tebl/RetroPanel/gallery/2022-11-07 02.01.57.jpg

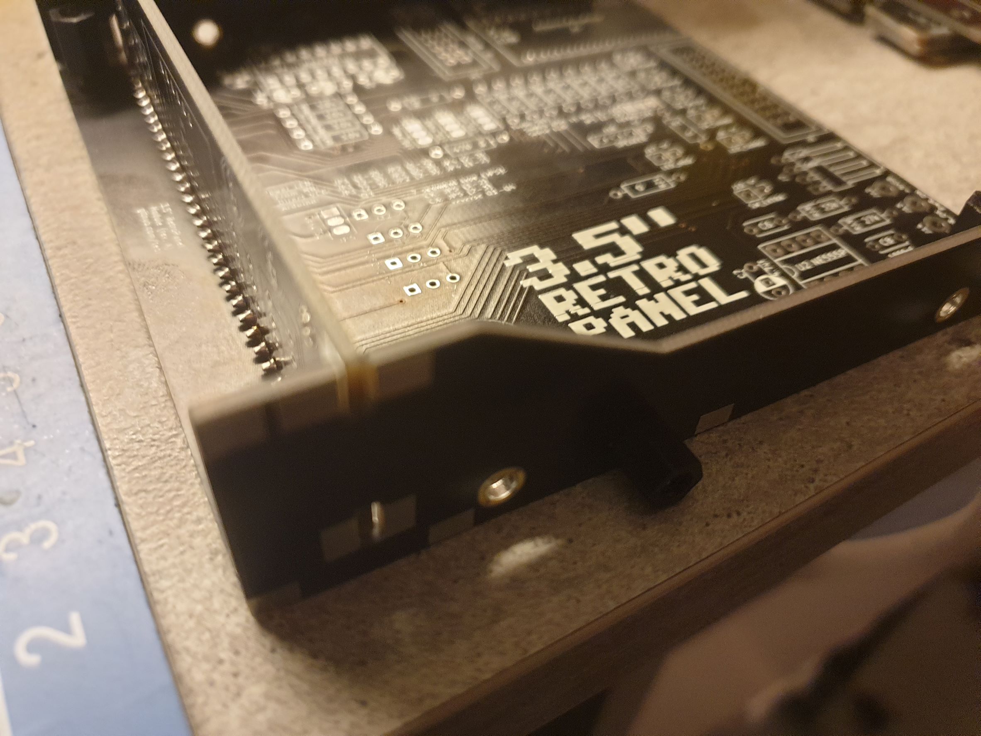
gallery/2022-11-07 02.01.57.jpg
