tebl/RetroPanel/gallery/2022-11-07 02.02.05.jpg

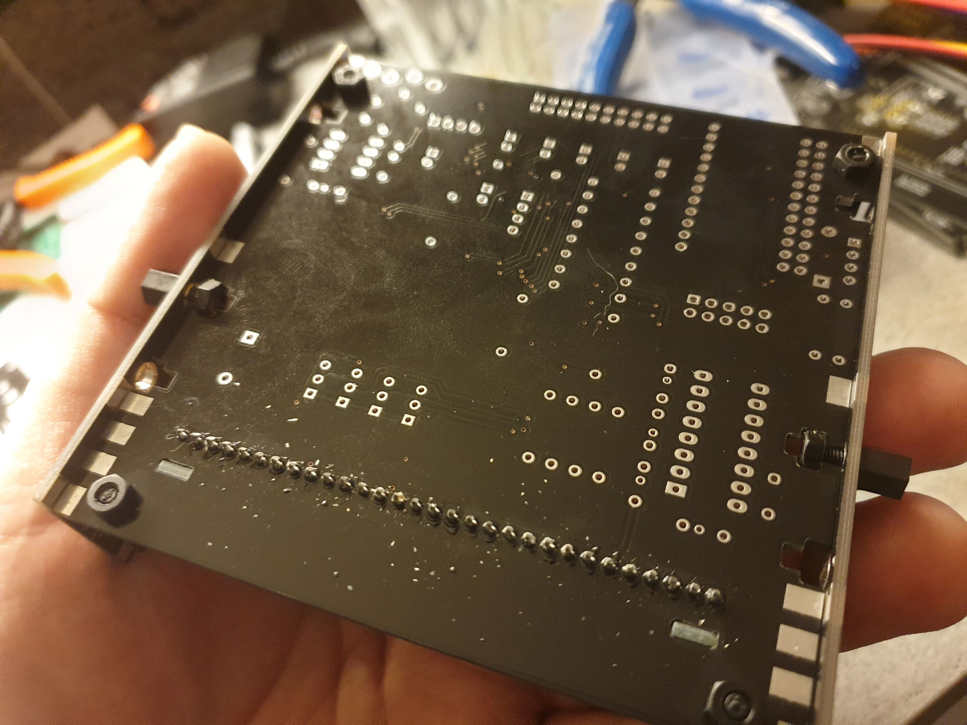
gallery/2022-11-07 02.02.05.jpg
