tebl/RetroPanel/gallery/2022-11-08 02.11.32.jpg

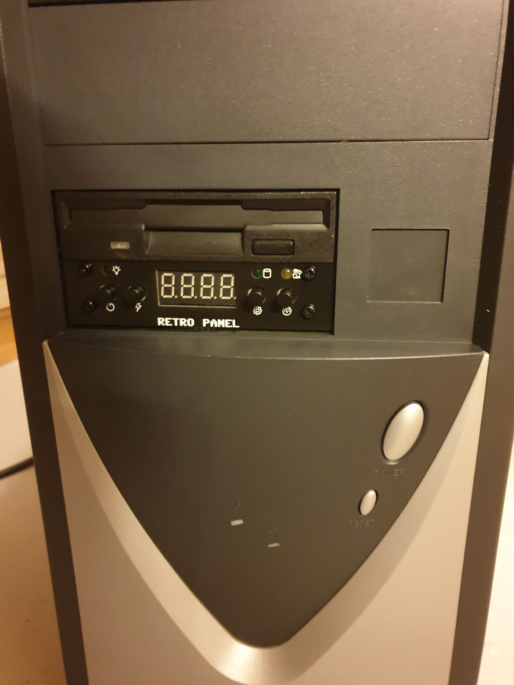
gallery/2022-11-08 02.11.32.jpg
