tebl/RetroPanel/gallery/2022-11-08 19.52.51.jpg

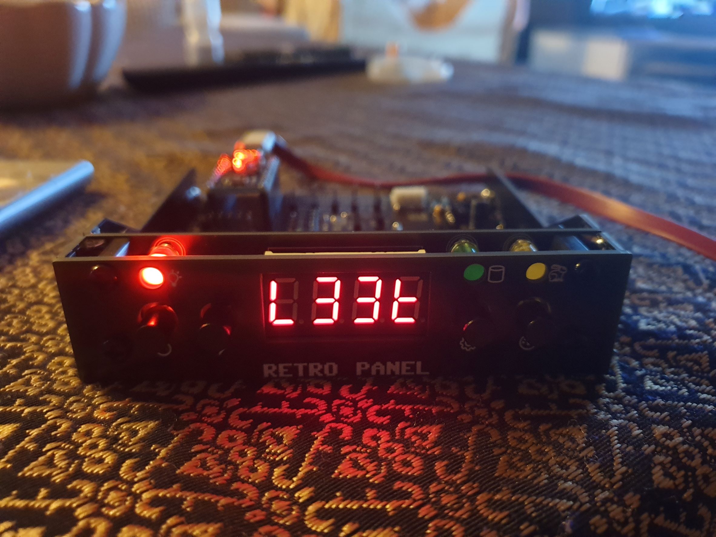
gallery/2022-11-08 19.52.51.jpg
