tebl/RetroPanel/gallery/2022-11-09 23.40.05.jpg

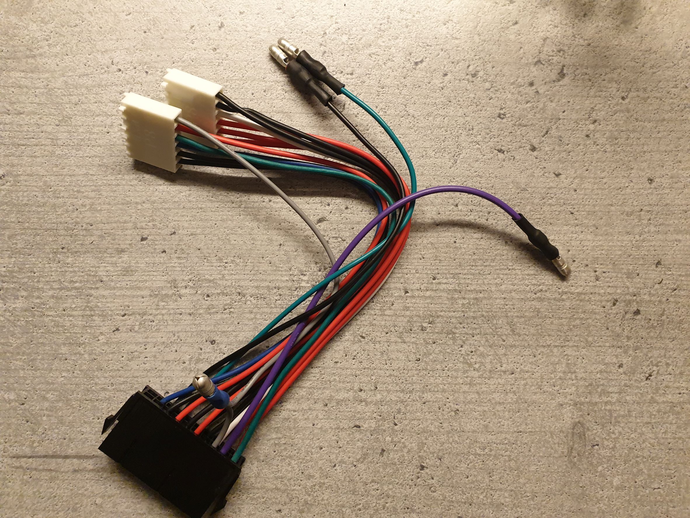
gallery/2022-11-09 23.40.05.jpg
