tebl/RetroPanel/gallery/2022-11-12 02.01.29.jpg

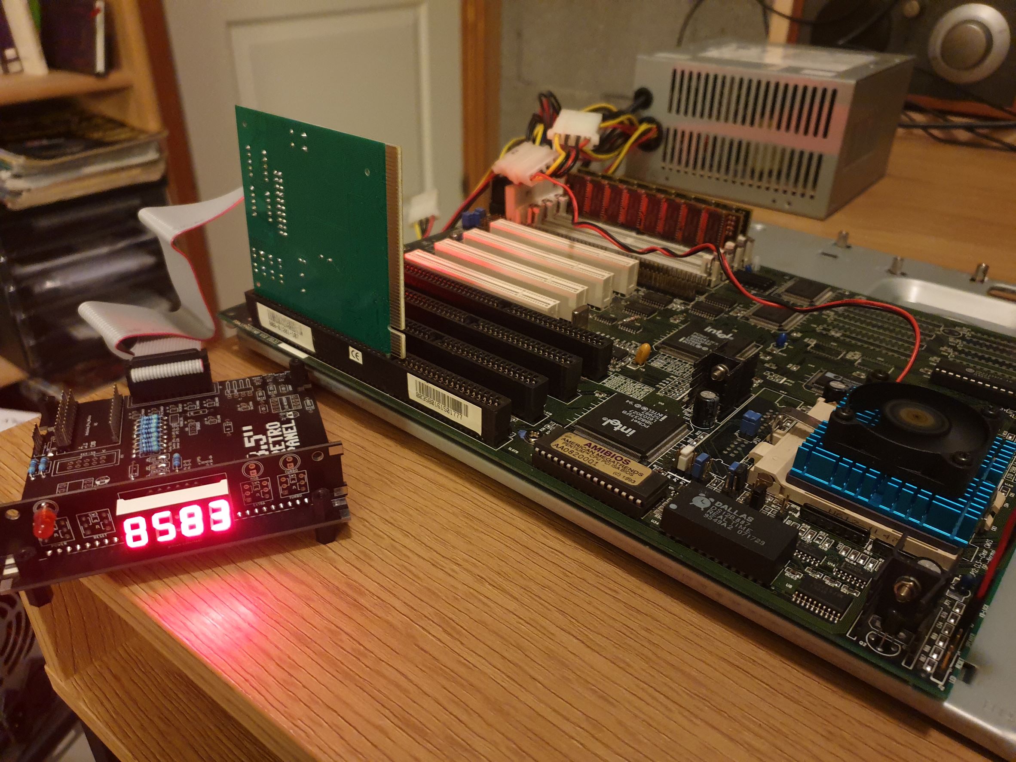
gallery/2022-11-12 02.01.29.jpg
