tebl/RetroPanel/gallery/2022-11-16 23.27.16.jpg

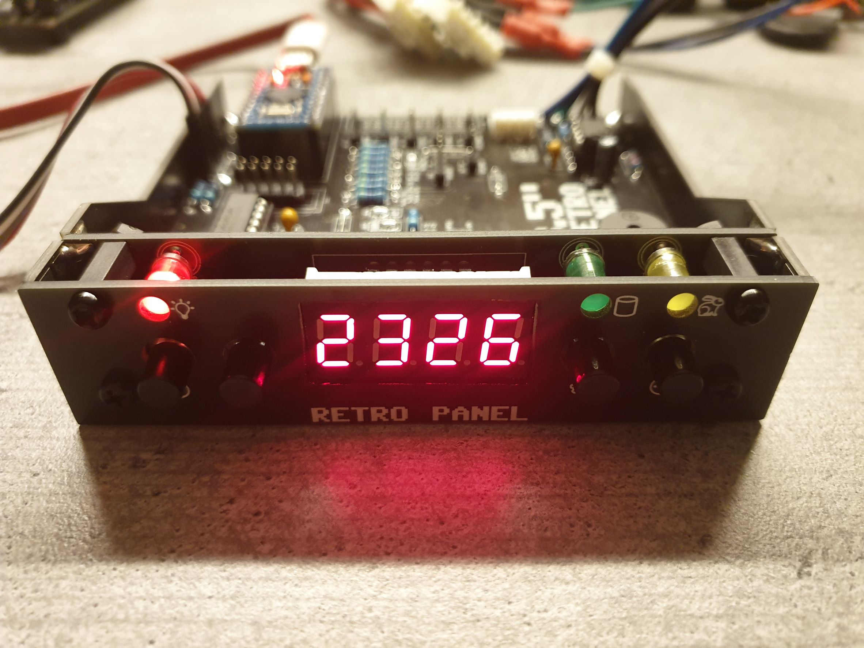
gallery/2022-11-16 23.27.16.jpg
