tebl/RetroPanel/gallery/2022-11-18 00.04.18.jpg

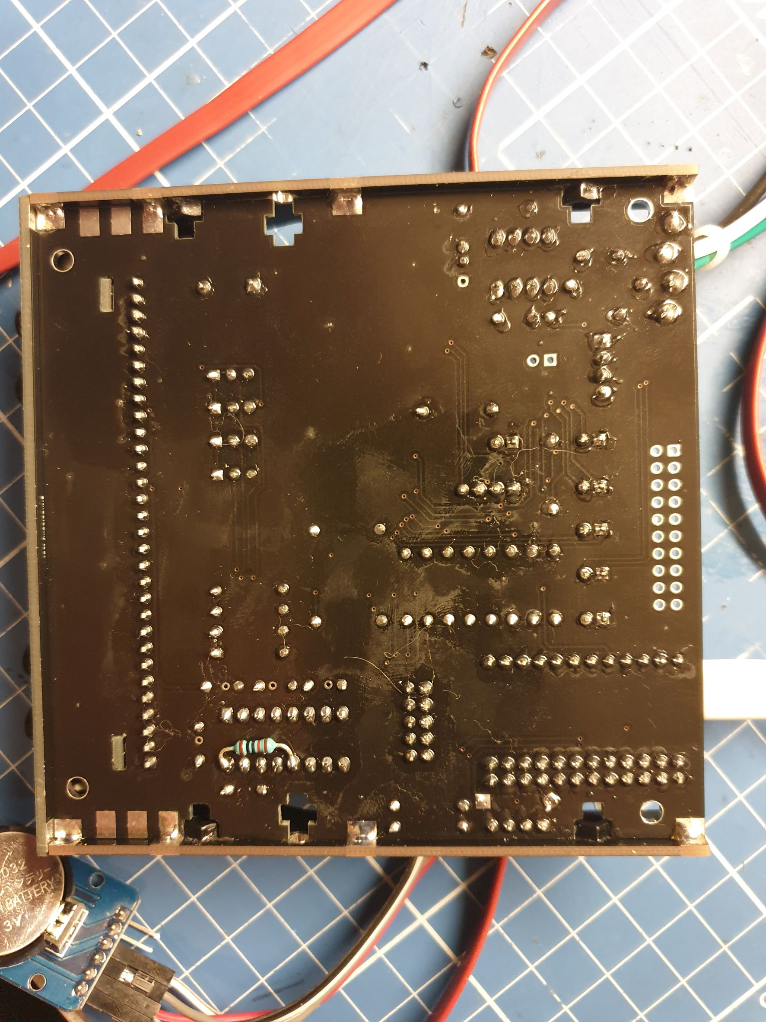
gallery/2022-11-18 00.04.18.jpg
