tebl/RetroPanel/gallery/2022-11-22 23.41.05.jpg

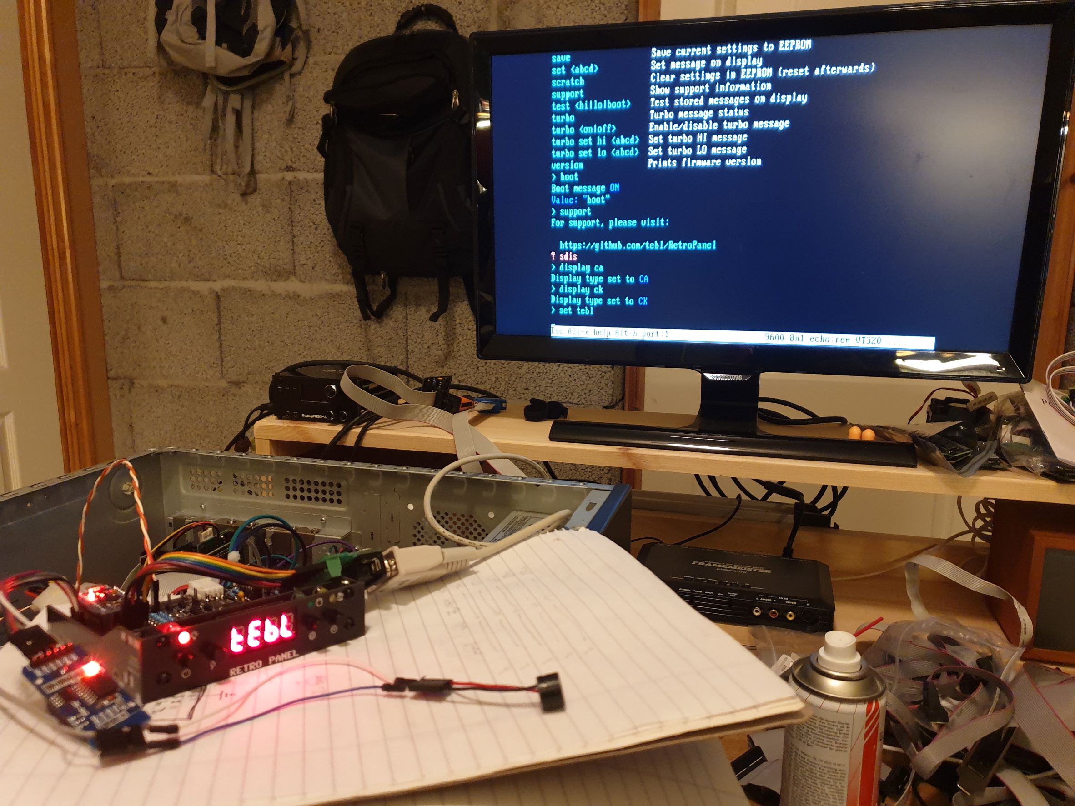
gallery/2022-11-22 23.41.05.jpg
