tebl/RetroPanel/gallery/2022-11-23 00.05.52.jpg

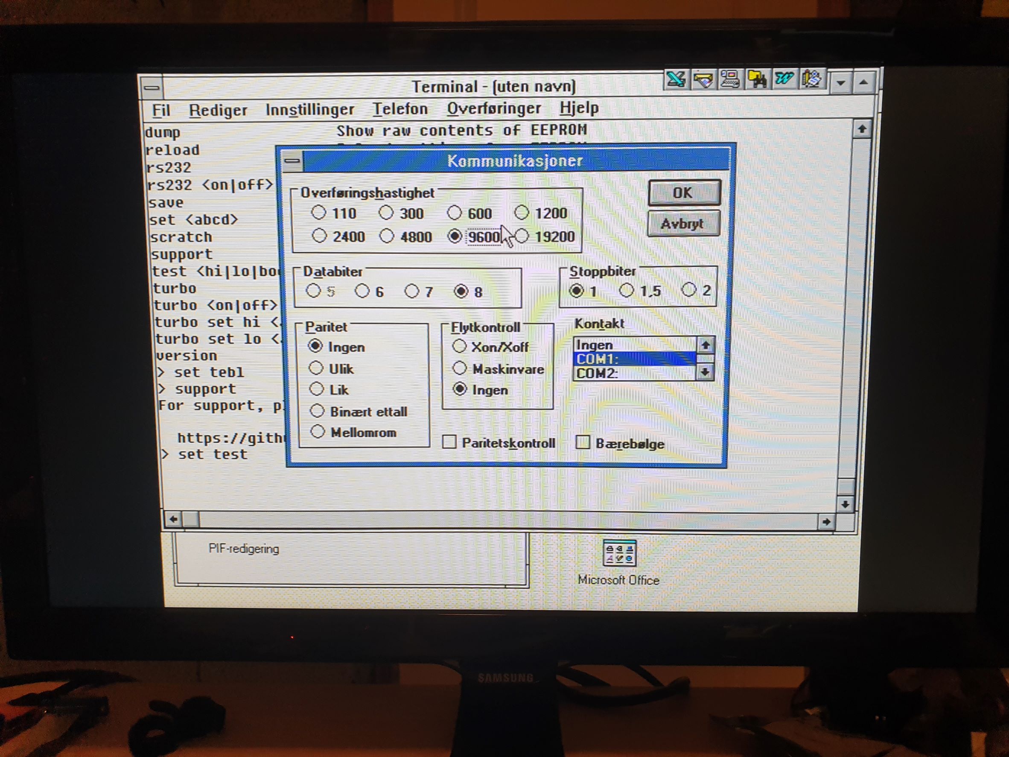
gallery/2022-11-23 00.05.52.jpg
