tebl/RetroPanel/gallery/2022-11-23 00.06.09.jpg

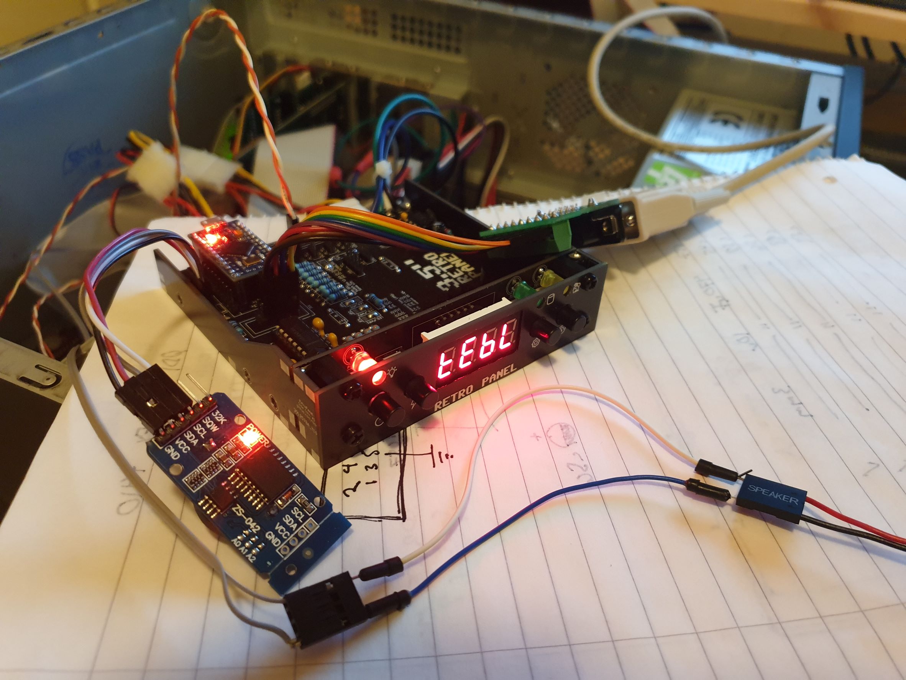
gallery/2022-11-23 00.06.09.jpg
