tebl/RetroPanel/gallery/2022-11-23 00.19.36.jpg

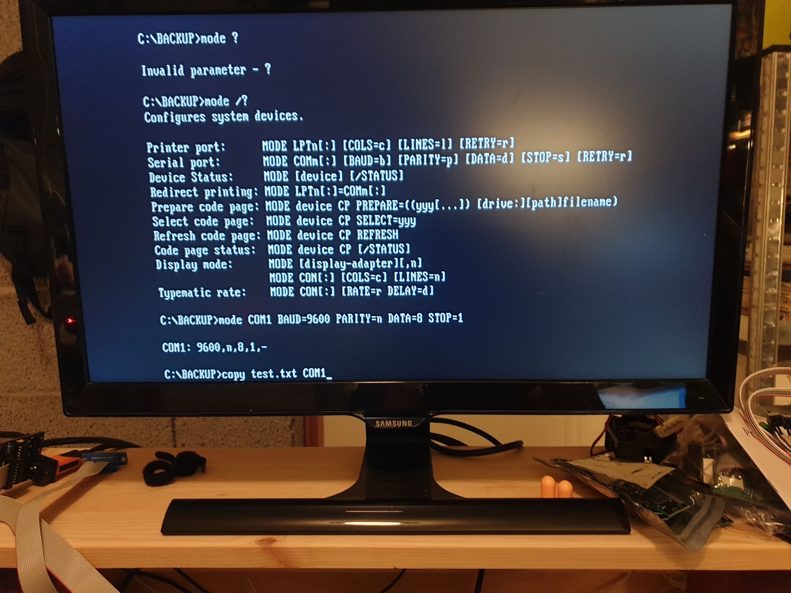
gallery/2022-11-23 00.19.36.jpg
