tebl/RetroPanel/gallery/2022-11-23 00.22.08.jpg

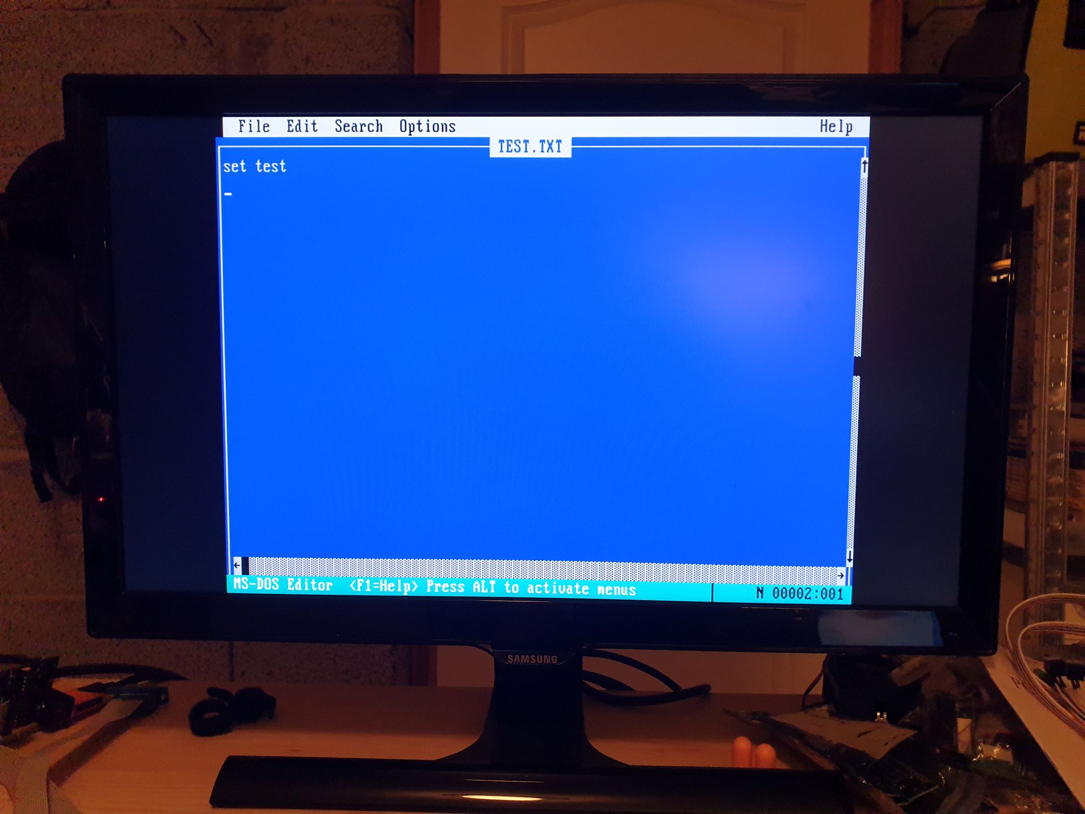
gallery/2022-11-23 00.22.08.jpg
