tebl/RetroPanel/gallery/2022-11-23 01.13.37.jpg

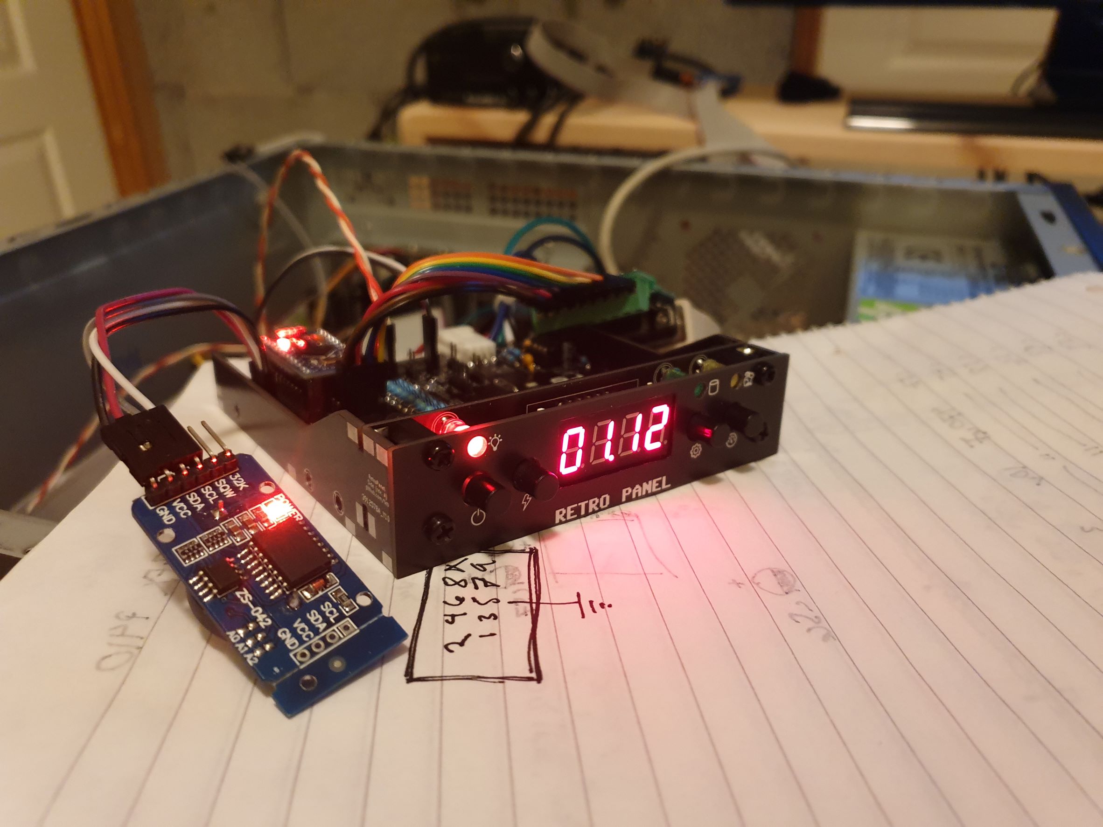
gallery/2022-11-23 01.13.37.jpg
