tebl/RetroPanel/gallery/2023-01-03 02.21.16.jpg

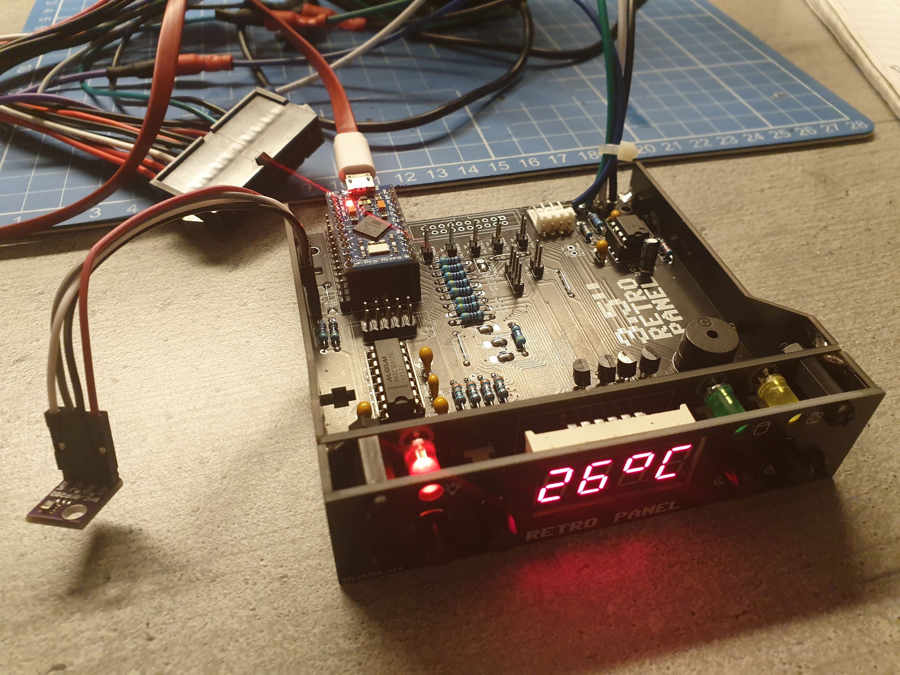
gallery/2023-01-03 02.21.16.jpg
