tebl/RetroPanel/gallery/2023-01-03 02.21.26.jpg

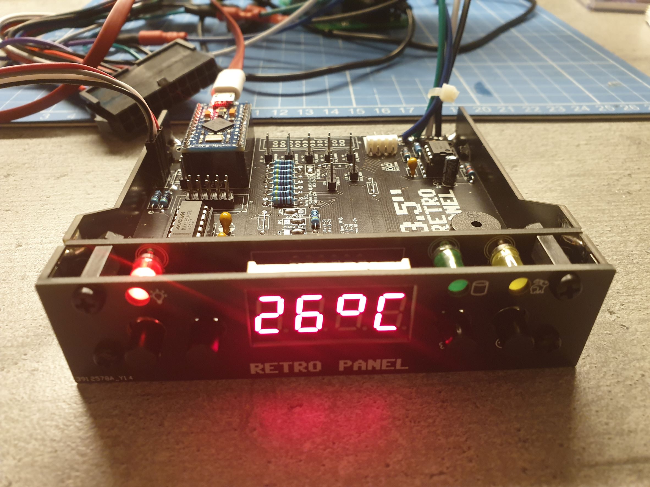
gallery/2023-01-03 02.21.26.jpg
