tebl/RetroPanel/gallery/2023-01-09 01.00.15.jpg

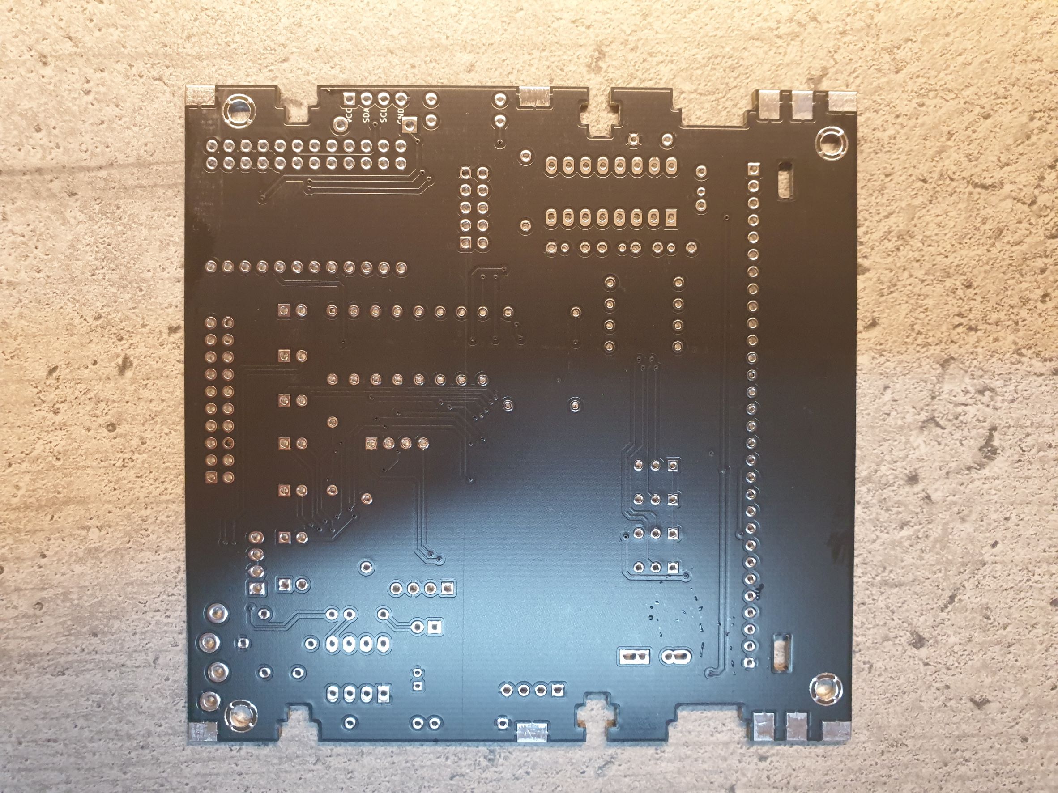
gallery/2023-01-09 01.00.15.jpg
