tebl/RetroPanel/gallery/2023-01-09 01.00.59.jpg

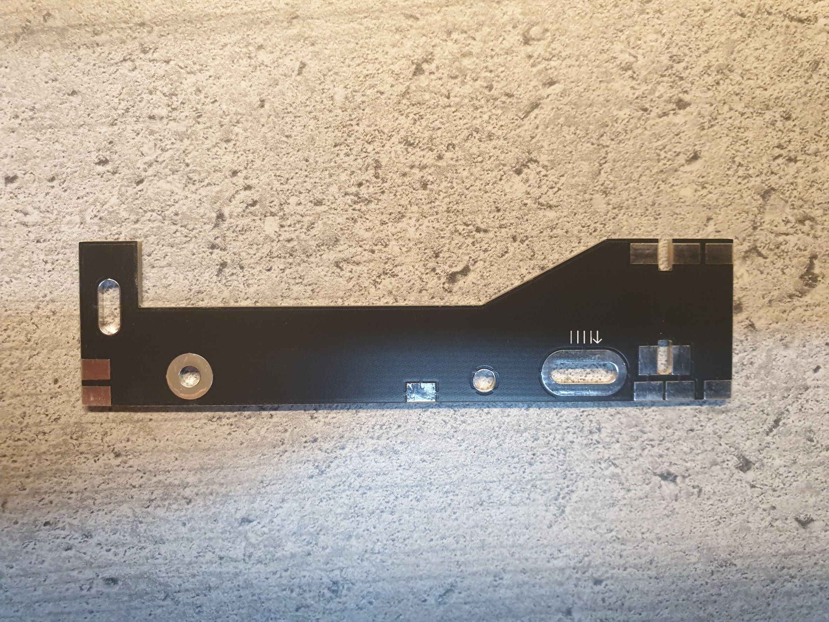
gallery/2023-01-09 01.00.59.jpg
