tebl/RetroPanel/gallery/2023-01-09 01.01.20.jpg

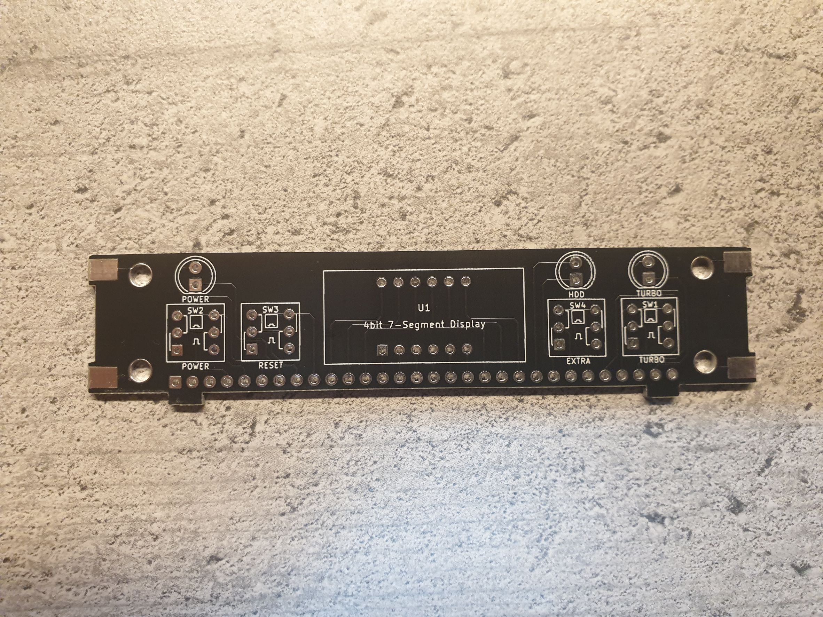
gallery/2023-01-09 01.01.20.jpg
