tebl/RetroPanel/gallery/2023-01-09 01.01.31.jpg

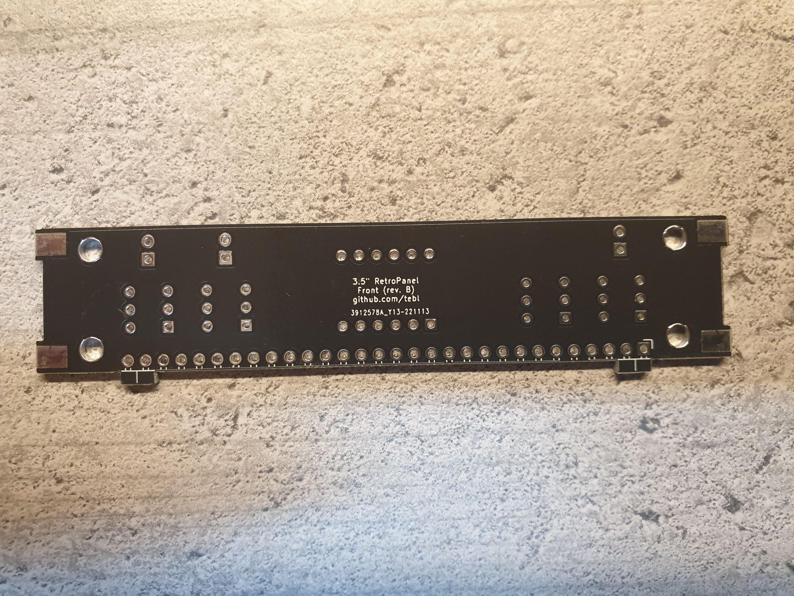
gallery/2023-01-09 01.01.31.jpg
