tebl/RetroPanel/gallery/2023-01-09 01.02.02.jpg

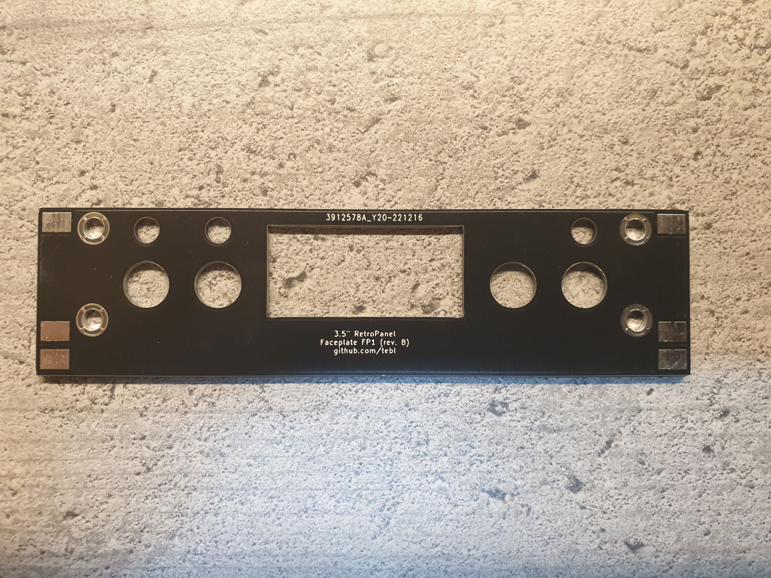
gallery/2023-01-09 01.02.02.jpg
