tebl/RetroPanel/gallery/2023-01-13 18.41.41.jpg

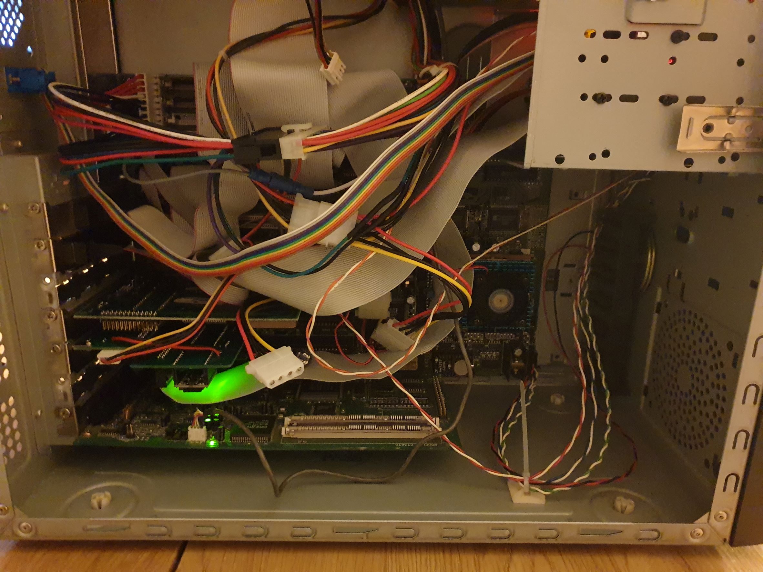
gallery/2023-01-13 18.41.41.jpg
