tebl/RetroPanel/gallery/2023-01-13 18.42.02.jpg

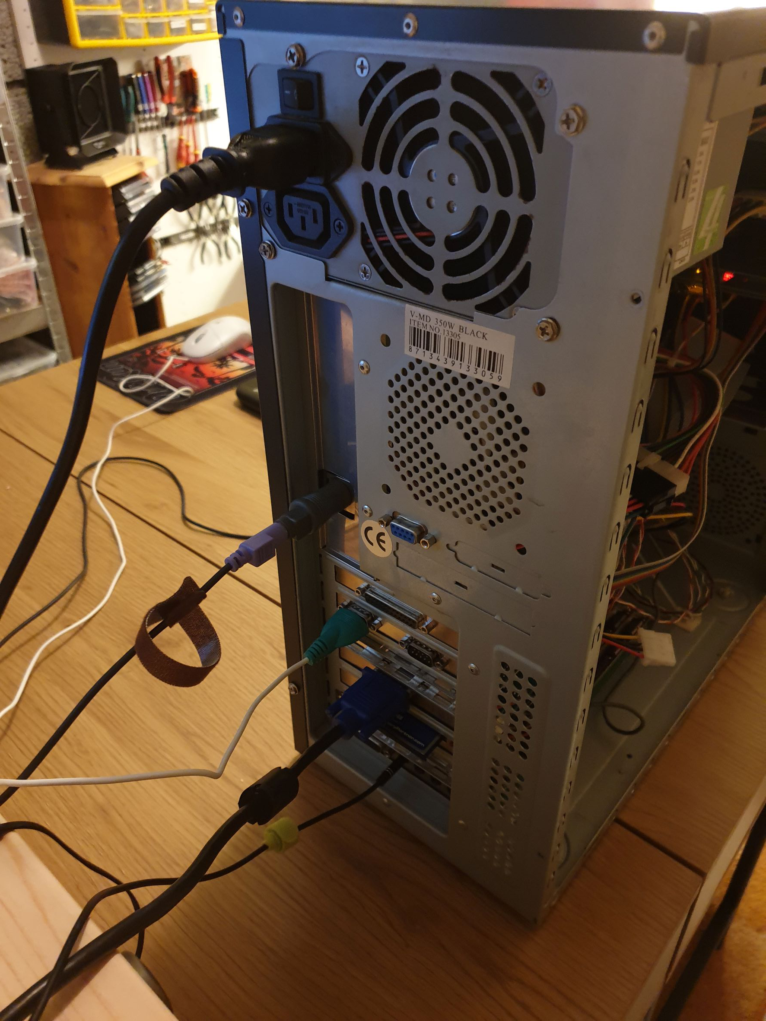
gallery/2023-01-13 18.42.02.jpg
