tebl/RetroPanel/gallery/2023-01-20 01.23.10.jpg

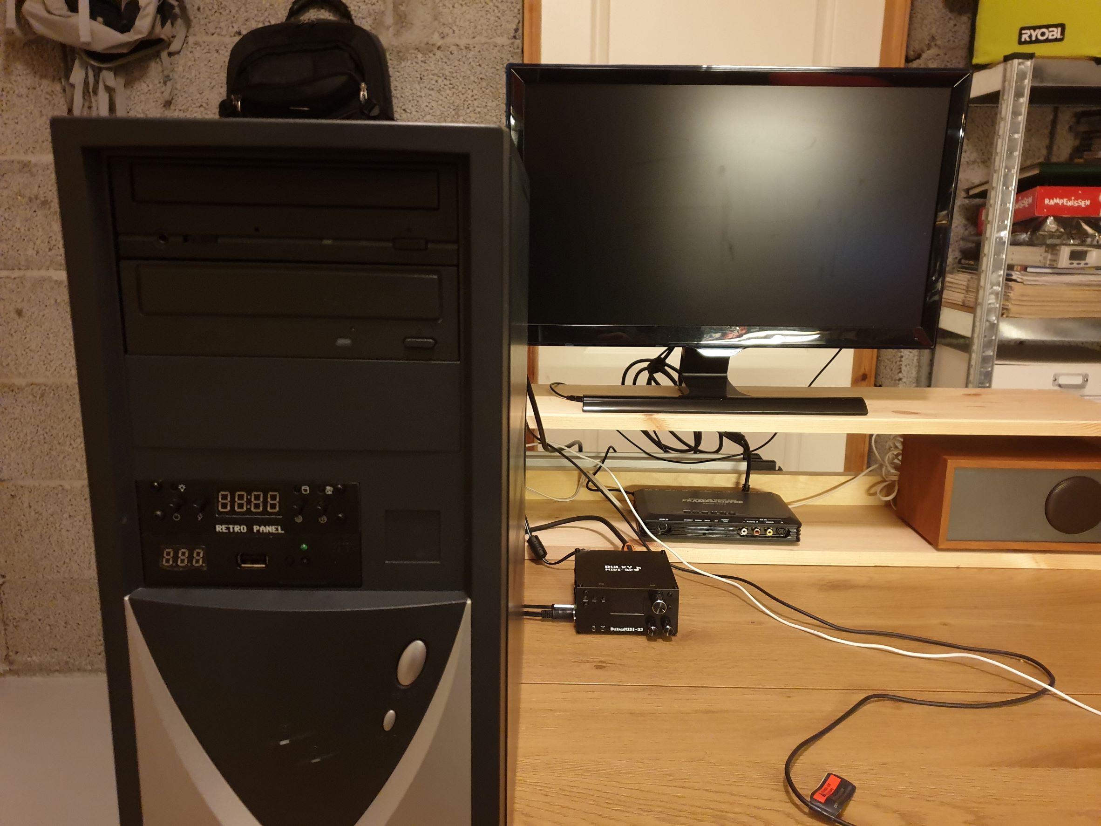
gallery/2023-01-20 01.23.10.jpg
