tebl/RetroPanel/gallery/2023-01-25 23.20.16.jpg

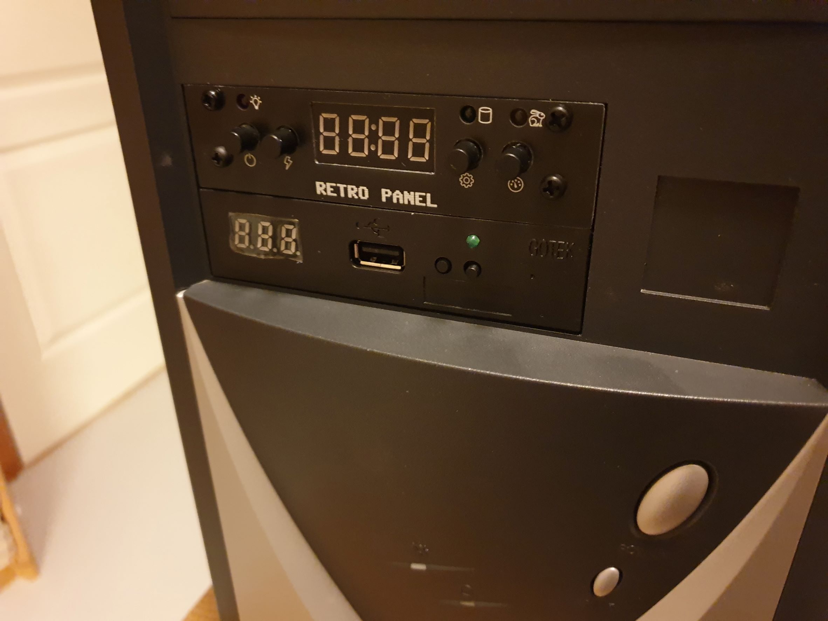
gallery/2023-01-25 23.20.16.jpg
