tebl/RetroPanel/gallery/2023-01-29 00.01.37.jpg

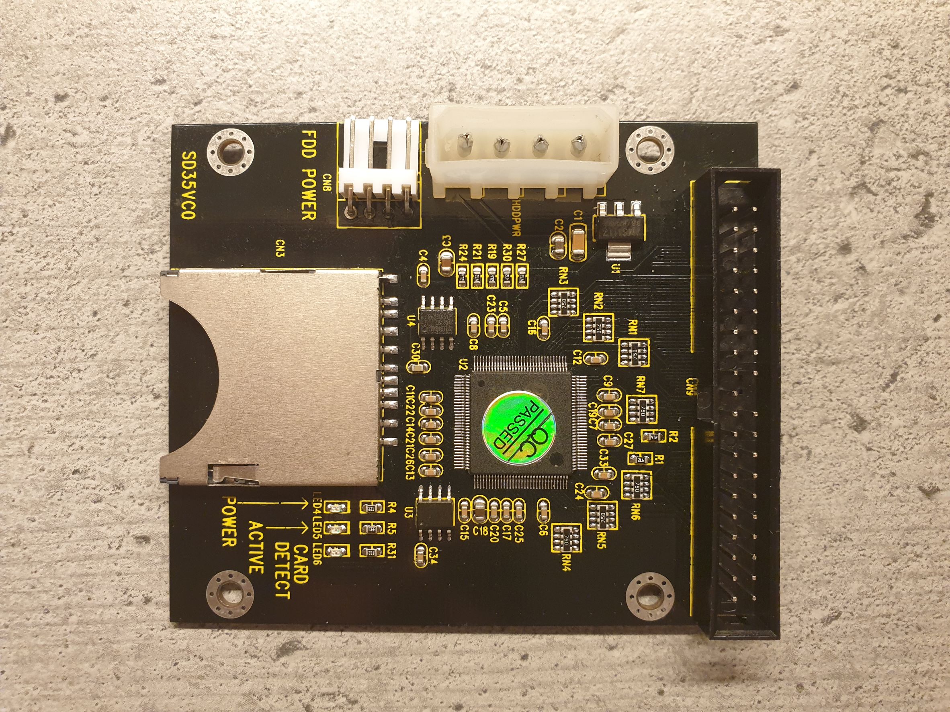
gallery/2023-01-29 00.01.37.jpg
