tebl/RetroPanel/gallery/2023-02-06 02.13.39.jpg

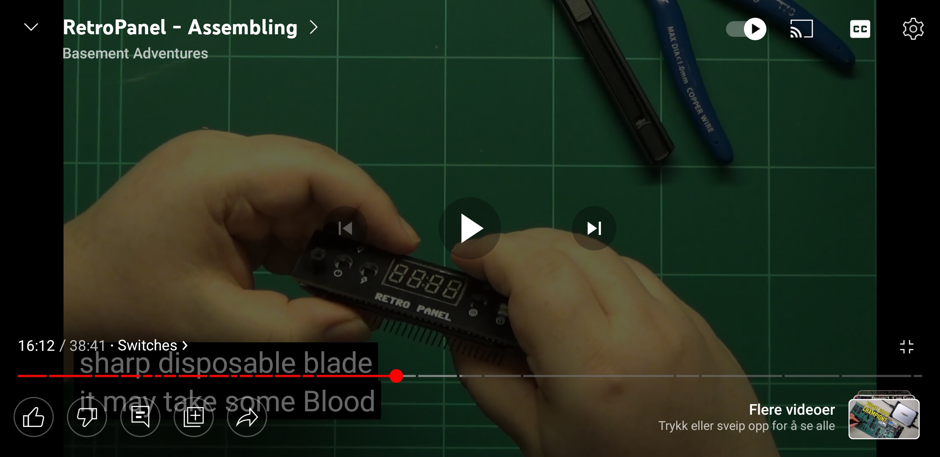
gallery/2023-02-06 02.13.39.jpg
