tebl/RetroPanel/gallery/RetroPanel Front.png

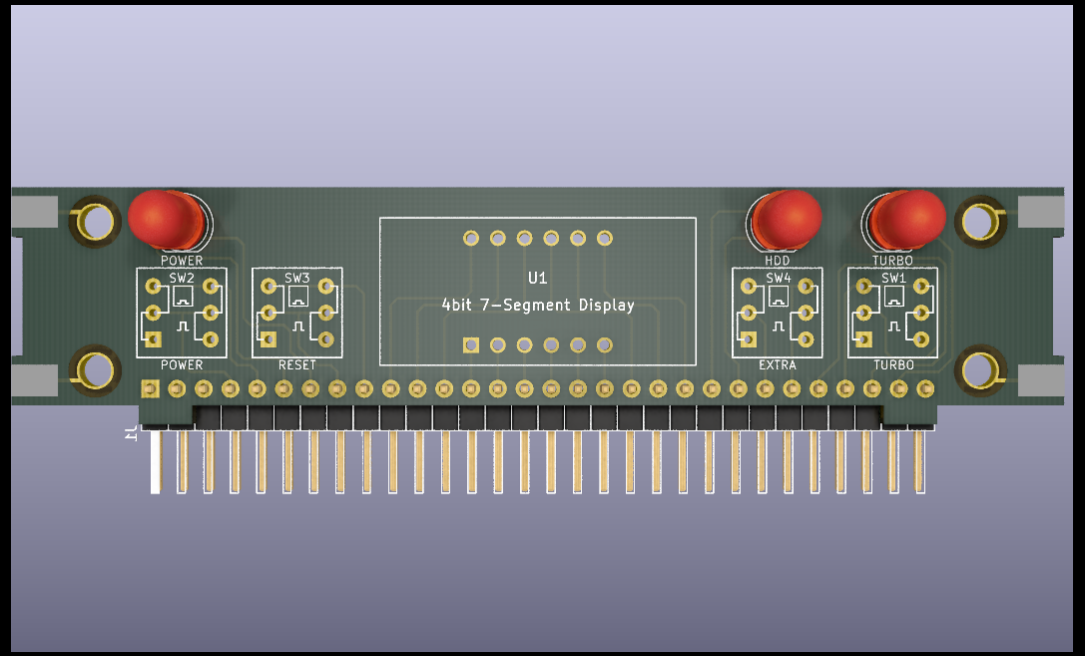
gallery/RetroPanel Front.png
