tebl/RetroPanel/gallery/RetroPanel Module.png

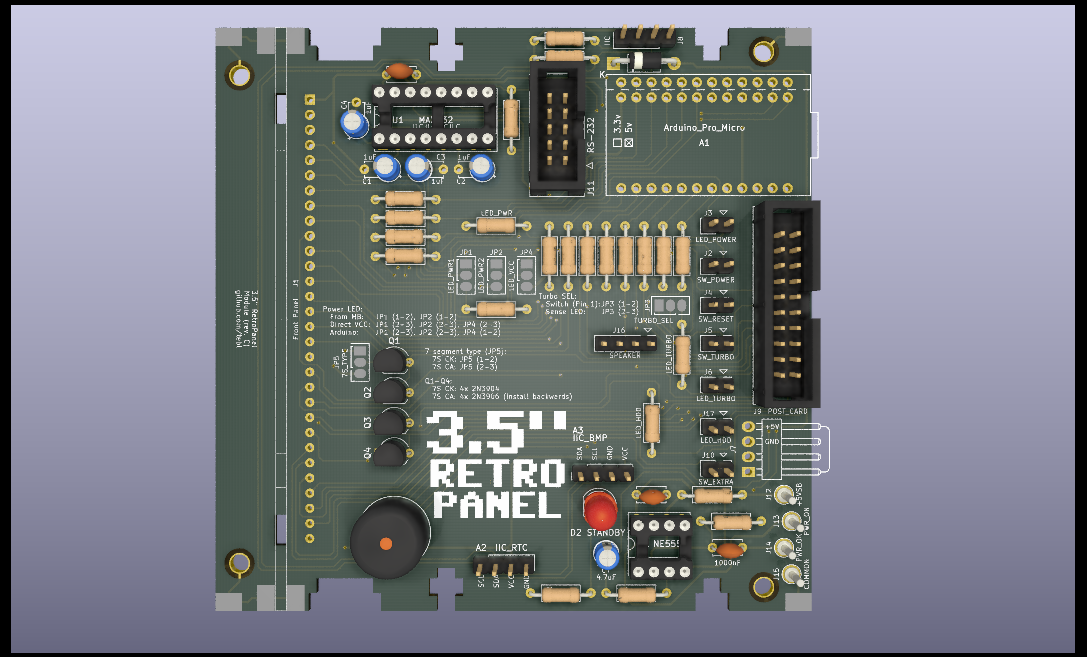
gallery/RetroPanel Module.png
