tebl/RetroPanel/gallery/RetroPanel SD35VC0 Front.png

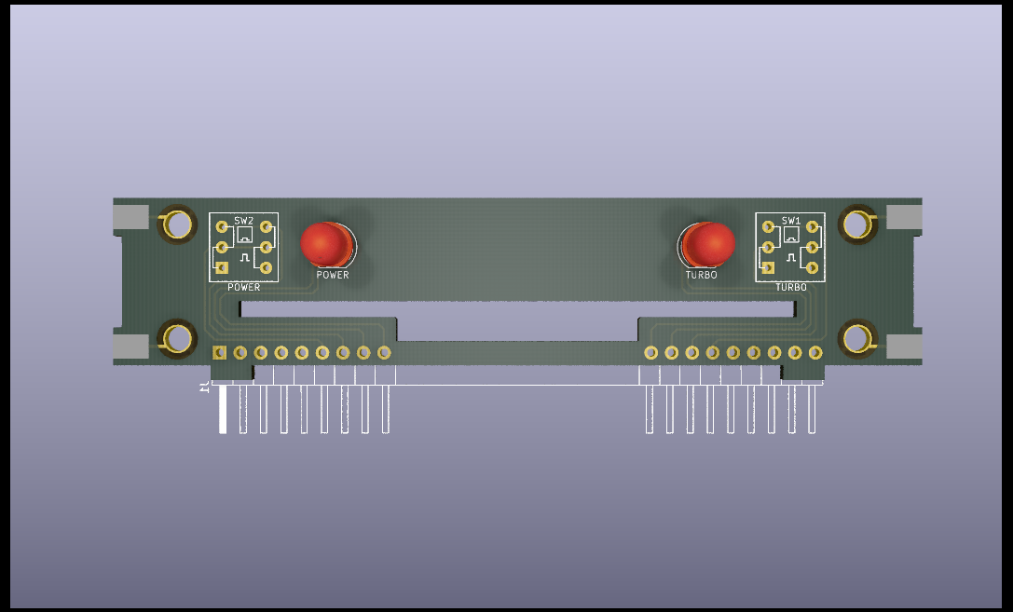
gallery/RetroPanel SD35VC0 Front.png
