tebl/RetroPanel/gallery/RetroPanel SD35VC0.png

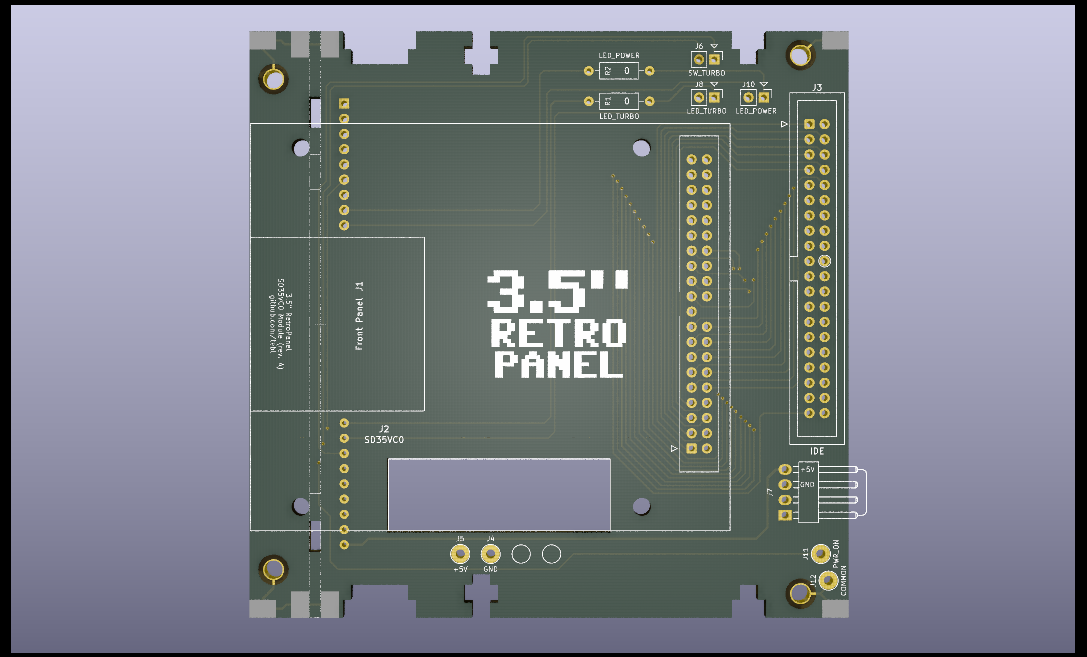
gallery/RetroPanel SD35VC0.png
