tebl/RetroPanel/gallery/RetroPanel Side.png

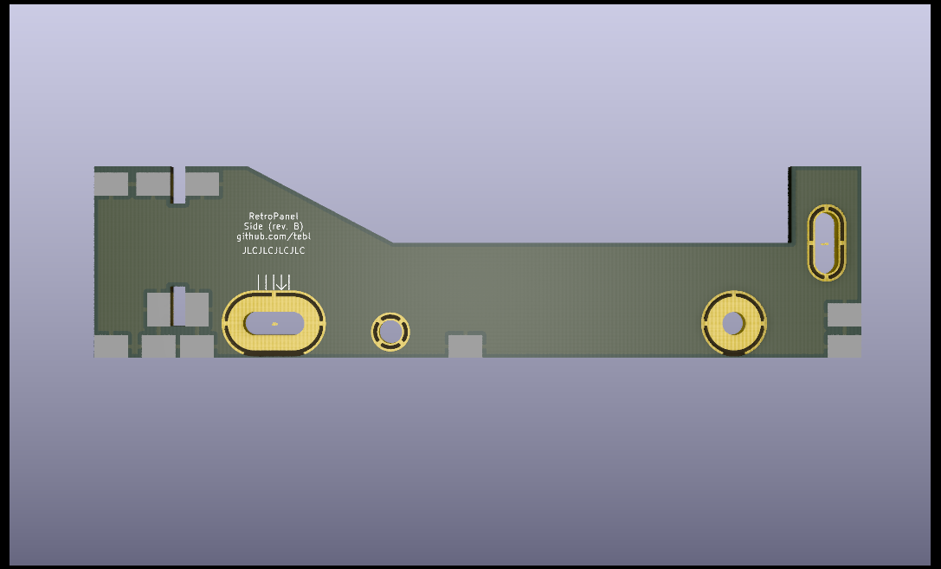
gallery/RetroPanel Side.png
