tebl/RetroPanel/gallery/build_002.jpg

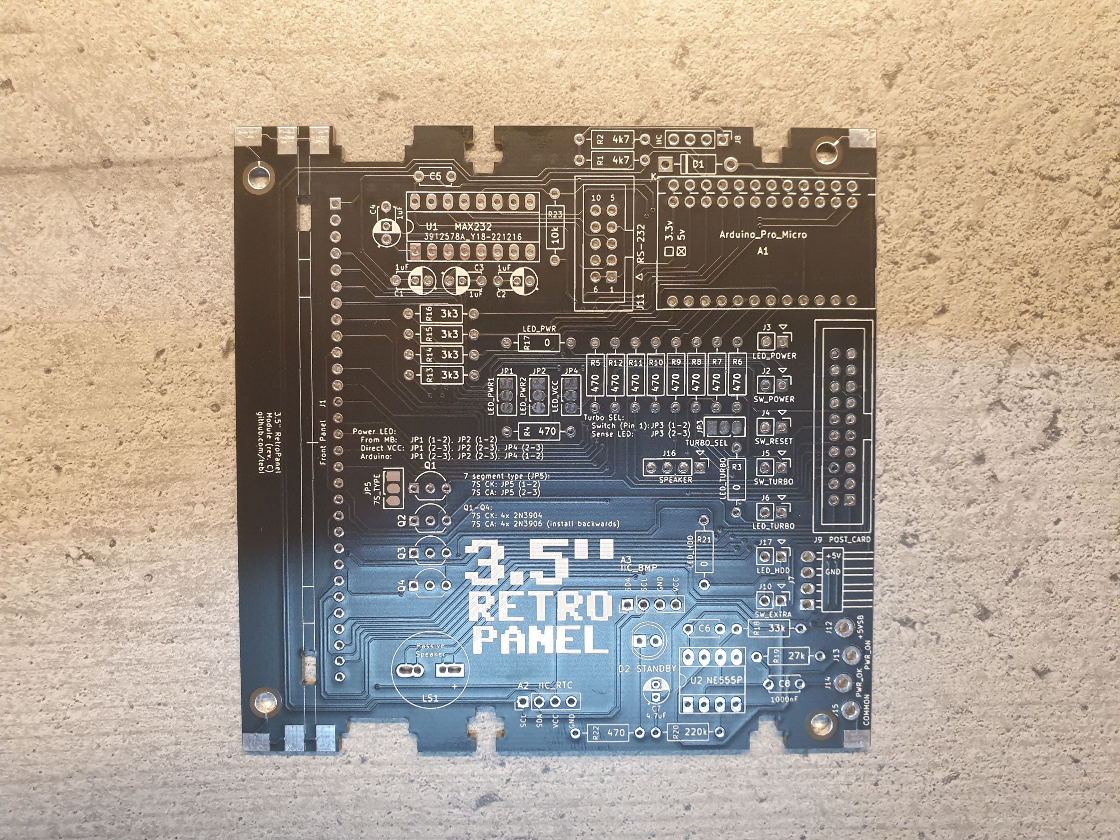
gallery/build_002.jpg
