tebl/RetroPanel/gallery/build_panel_001.jpg

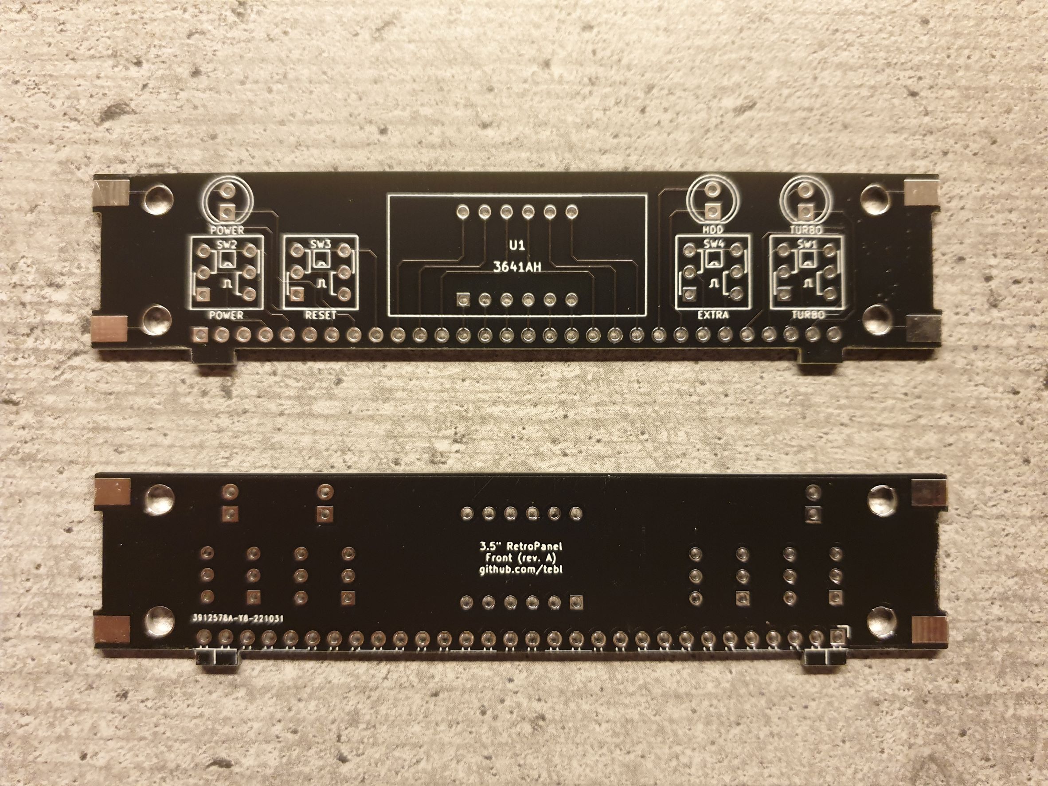
gallery/build_panel_001.jpg
